whutddk/LED256/pic/2014_10_11_22_08_38.jpg

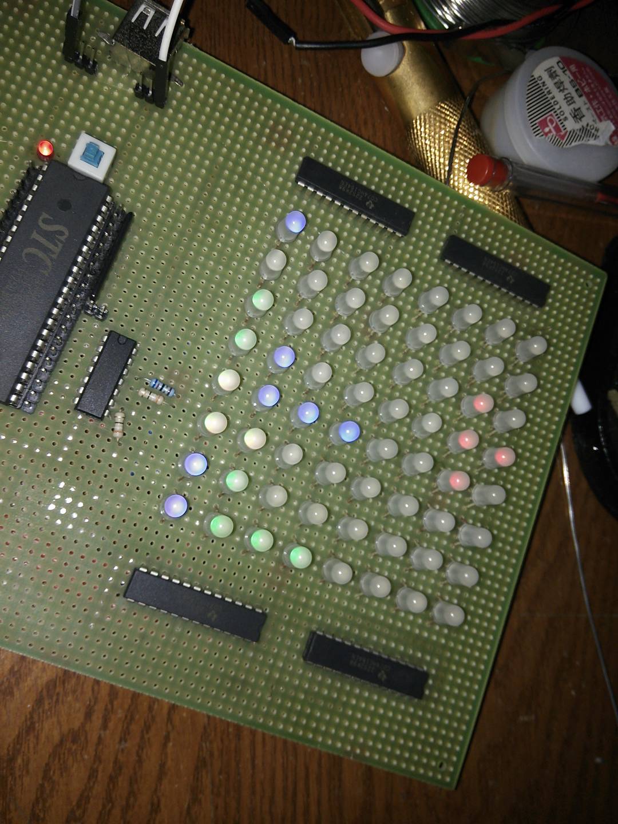
pic/2014_10_11_22_08_38.jpg
