whutddk/LED256/pic/2014_10_11_22_08_57.jpg

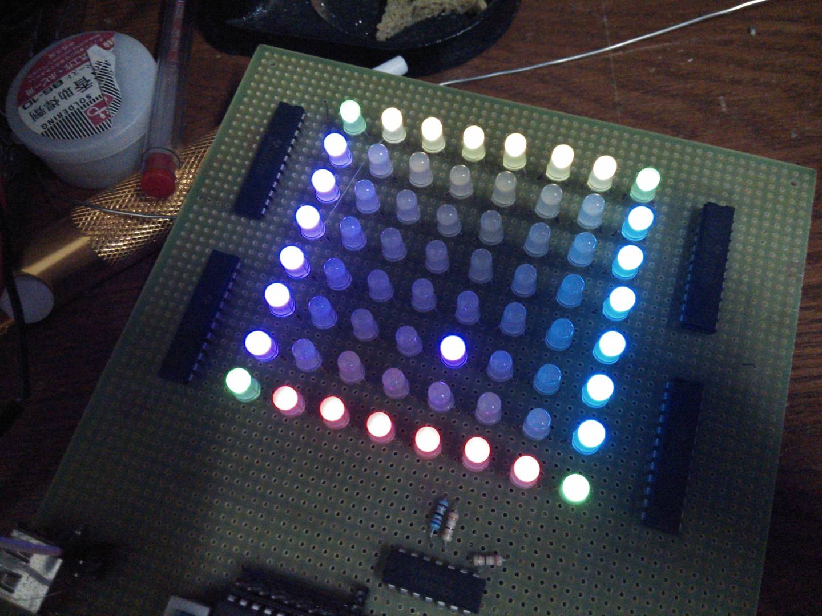
pic/2014_10_11_22_08_57.jpg
