whutddk/LED256/pic/IMG_20140204_224755_SHOT2SHOT6.jpg

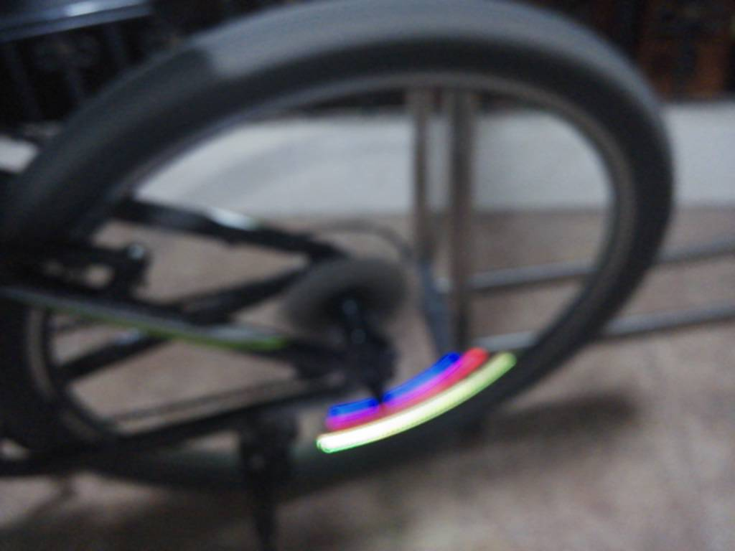
pic/IMG_20140204_224755_SHOT2SHOT6.jpg
