whutddk/LED256/pic/IMG_20140207_230346_SHOT2SHOT12.jpg

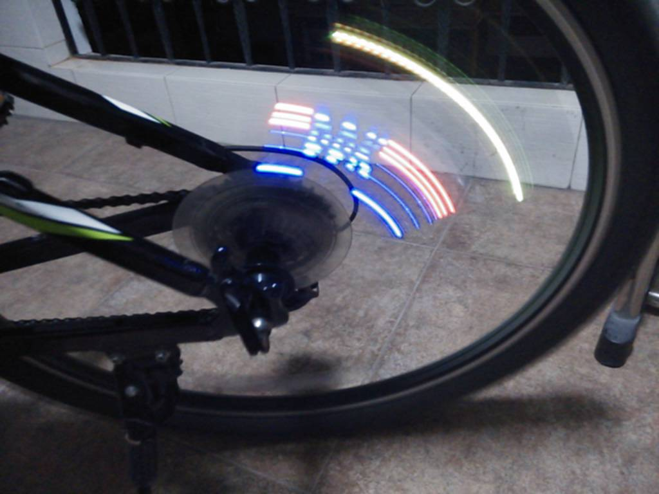
pic/IMG_20140207_230346_SHOT2SHOT12.jpg
