whutddk/LED256/pic/IMG_20140207_230420_SHOT2SHOT11.jpg

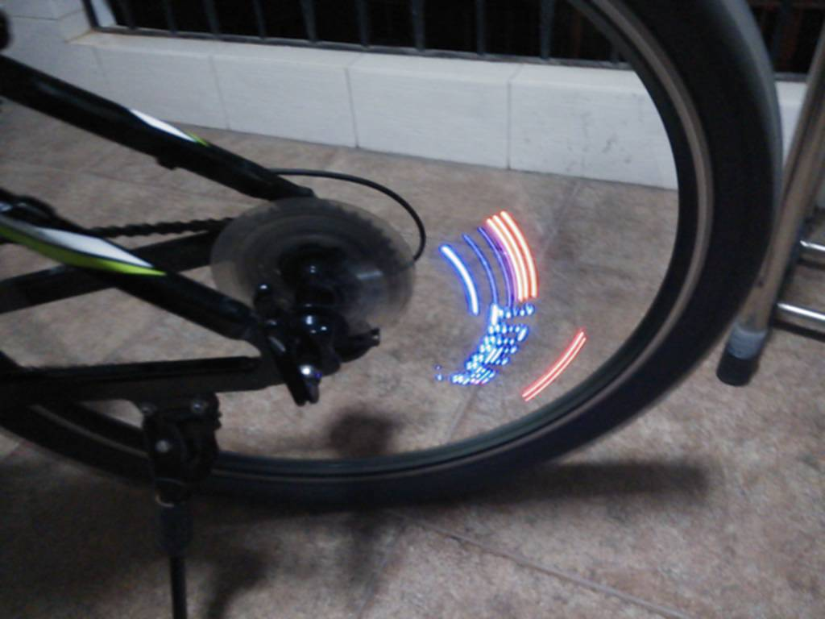
pic/IMG_20140207_230420_SHOT2SHOT11.jpg
