whutddk/LED256/pic/IMG_20140207_230420_SHOT2SHOT20.jpg

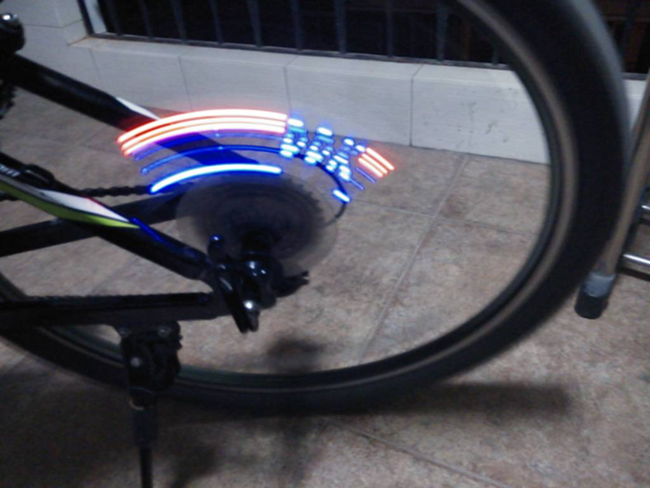
pic/IMG_20140207_230420_SHOT2SHOT20.jpg
