whutddk/LED256/pic/微信图片_2019013121595610.jpg

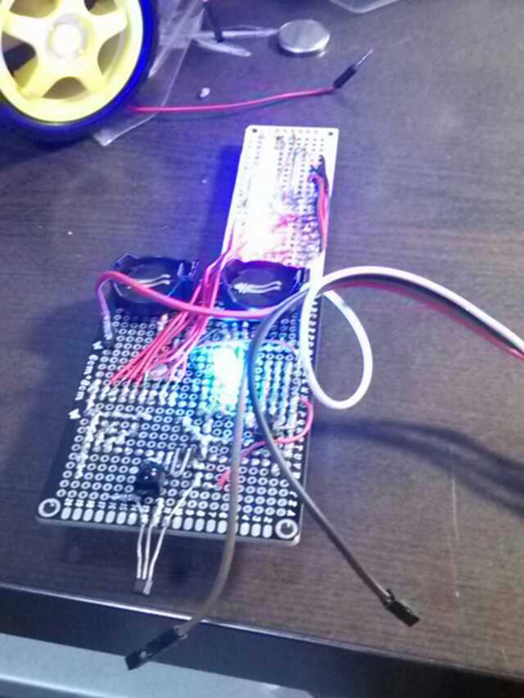
pic/微信图片_2019013121595610.jpg
