whutddk/LED256/pic/微信图片_2019013121595620.jpg

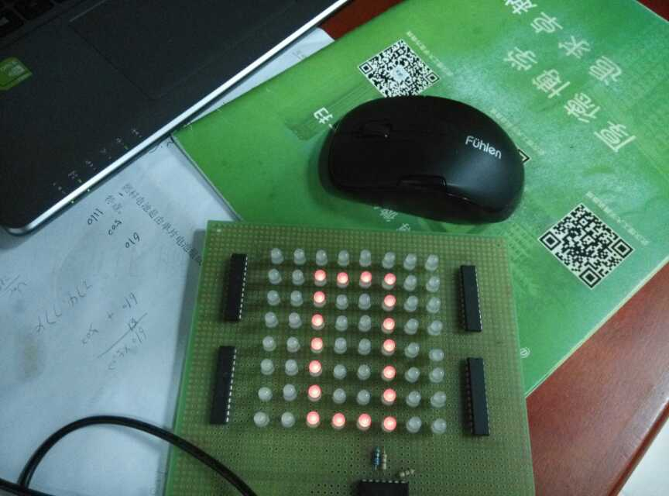
pic/微信图片_2019013121595620.jpg
